PE5PVB/SI4684-DAB-Receiver/src/Si468xROM.h

const PROGMEM unsigned char rom_patch_016[] = {
	0x10, 0x00, 0x00, 0xff, 0x00, 0x00, 0x00, 0x00, 0x00, 0x00, 0x00, 0x00, 0x78, 0x56, 0x34, 0x12, 
	0x00, 0x00, 0x00, 0x00, 0x00, 0x00, 0x00, 0x00, 0xfd, 0x84, 0xcb, 0x6c, 0x01, 0x00, 0x00, 0x00, 
	0xef, 0xbe, 0xad, 0xde, 0x48, 0x16, 0x00, 0x00, 0x04, 0x00, 0x00, 0x00, 0x04, 0x00, 0x00, 0x00, 
	0x00, 0x00, 0x00, 0x00, 0x44, 0x05, 0x20, 0x50, 0x00, 0x00, 0x00, 0x00, 0x00, 0x00, 0x00, 0x00, 
	0x00, 0x00, 0x00, 0x00, 0x00, 0x00, 0x00, 0x00, 0x00, 0x00, 0x00, 0x00, 0x00, 0x00, 0x00, 0x00, 
	0x00, 0x00, 0x00, 0x00, 0x88, 0xcf, 0x6f, 0x07, 0x6f, 0x00, 0x00, 0x81, 0x00, 0xd8, 0x00, 0x50, 
	0x48, 0xe0, 0x00, 0x50, 0x50, 0xe1, 0x00, 0x50, 0x00, 0x2a, 0x00, 0x50, 0xac, 0x67, 0x28, 0x50, 
	0x6c, 0x65, 0x28, 0x50, 0x00, 0x2e, 0x00, 0xa0, 0x80, 0x2a, 0x00, 0x50, 0xa0, 0x96, 0x28, 0x50, 
	0x0c, 0xff, 0xf0, 0xff, 0x00, 0x1e, 0x00, 0xa0, 0x80, 0xff, 0xff, 0x4f, 0xe8, 0x95, 0x28, 0x50, 
	0x40, 0x00, 0x00, 0x50, 0xf8, 0x92, 0x28, 0x50, 0x50, 0x00, 0x00, 0x50, 0x60, 0x00, 0x00, 0x50, 
	0x00, 0x00, 0xff, 0xff, 0x03, 0x10, 0x00, 0x00, 0xa8, 0x08, 0x20, 0x50, 0xc8, 0x08, 0x20, 0x50, 
	0x74, 0x08, 0x20, 0x50, 0xe0, 0x07, 0x20, 0x50, 0xf0, 0x09, 0x20, 0x50, 0x60, 0x06, 0x20, 0x50, 
	0x00, 0xfe, 0x00, 0x50, 0x03, 0x04, 0x20, 0x90, 0xfc, 0x08, 0x20, 0x50, 0x78, 0x67, 0x28, 0x50, 
	0x50, 0x2a, 0x00, 0x50, 0x00, 0x22, 0x00, 0x50, 0xff, 0xff, 0x1f, 0x50, 0x00, 0x00, 0x26, 0x50, 
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
	0x43, 0x54, 0x4e, 0x3e, 0x0a, 0x00, 0x00, 0x00, 0x42, 0x00, 0x00, 0x21, 0x48, 0xe0, 0x00, 0x50, 
	0x0a, 0x05, 0x00, 0x80, 0x00, 0x04, 0x20, 0x50, 0x36, 0x41, 0x00, 0x21, 0x02, 0x32, 0xc0, 0x20, 
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
};
// End of Block 1


  
