PE5PVB/SI4684-DAB-Receiver/src/si4684.h

// Driver for the Skyworks (formerly Silicon Labs) SI4684 DAB+ receiver chip.
//
// Communicates over SPI (pins set up in begin()). Boots the chip by uploading
// the rom-patch + firmware blob, then exposes high-level operations:
//   - tune to a DAB Band III channel
//   - enumerate the services in the current ensemble
//   - select a service and start audio
//   - decode Dynamic Label / Radiotext, PTY, ECC, time, etc.
//   - reassemble MOT slideshow images into /slideshow.img on LittleFS
//
// All chip status comes back via the SPI status byte + a 4 KB SPI rx buffer
// (`SPIbuffer` in si4684.cpp). Every command goes via cts() to wait for the
// "command ready" bit before the next byte is written.

#ifndef si4684_h
#define si4684_h

#include "Arduino.h"
#include <LittleFS.h>
#include "Si468xROM.h"
#include "firmware.h"
#include <SPI.h>
#include <cstring>
#include <climits>

struct DABFrequencyLabel_DAB {
  uint32_t frequency;
  const char* label;
};

const DABFrequencyLabel_DAB DABfrequencyTable_DAB[] = {
  { 174928,  "5A"}, { 176640,  "5B"}, { 178352,  "5C"}, { 180064,  "5D"},
  { 181936,  "6A"}, { 183648,  "6B"}, { 185360,  "6C"}, { 187072,  "6D"},
  { 188928,  "7A"}, { 190640,  "7B"}, { 192352,  "7C"}, { 194064,  "7D"},
  { 195936,  "8A"}, { 197648,  "8B"}, { 199360,  "8C"}, { 201072,  "8D"},
  { 202928,  "9A"}, { 204640,  "9B"}, { 206352,  "9C"}, { 208064,  "9D"},
  { 209936, "10A"}, { 211648, "10B"}, { 213360, "10C"}, { 215072, "10D"},
  { 216928, "11A"}, { 218640, "11B"}, { 220352, "11C"}, { 222064, "11D"},
  { 223936, "12A"}, { 225648, "12B"}, { 227360, "12C"}, { 229072, "12D"},
  { 230784, "13A"}, { 232496, "13B"}, { 234208, "13C"}, { 235776, "13D"},
  { 237488, "13E"}, { 239200, "13F"}
};


static const char* const ProtectionText[] {
  "",
  "UEP-1",
  "UEP-2",
  "UEP-3",
  "UEP-4",
  "UEP-5",
  "EEP-A1",
  "EEP-A2",
  "EEP-A3",
  "EEP-A4",
  "EEP-B1",
  "EEP-B2",
  "EEP-B3",
  "EEP-B4"
};

static const char* const AudioModeText[] {
  "Dual",
  "Mono",
  "Stereo",
  "Joint stereo"
};

static const char* const ServiceTypeText[] {
  "TPEG",
  "Data",
  "FIDC",
  "MSC",
  "DAB+",
  "DAB",
  "FIC",
  "XPAD",
  "-",
  ""
};

// One row of the in-memory service table populated by ServiceInfo().
// Only one CompID per service is stored; secondary components (e.g. data
// streams in the same service) are intentionally ignored.
typedef struct _Services {
  uint32_t  ServiceID;
  uint32_t  CompID;
  char      Label[17];
  byte    ServiceType;
} DABService;

class DAB {
  public:
    bool begin(uint8_t SSpin);
    bool BufferSlideShow;
    bool panic(void);
    bool ServiceStart;
    bool signallock;
    bool SlideShowAvailable;
    bool SlideShowDebug;
    bool SlideShowUpdate;
    bool SlideShowUpdate2;
    char EID[5];
    char EnsembleLabel[17];
    char PStext[17];
    char ServiceData[128];
    char SID[5];
    char* getChipID(void);
    char* getFirmwareVersion(void);
    const char* getChannel(uint8_t freq);
    DABService service[32];
    String ASCII(const char* input, uint8_t charset);
    uint16_t bitrate;
    uint16_t ecc;
    uint16_t ensembleEcc;
    bool serviceHasOwnEcc;
    uint16_t getRSSI(void);
    uint16_t samplerate;
    uint16_t Year;
    uint32_t getFreq(uint8_t freq);
    uint32_t SlideShowLength;
    uint8_t audiomode;
    uint8_t cnr;
    uint8_t Days;
    uint8_t EnsembleLabelCharset;
    uint8_t fic;
    uint8_t getFIC(void);
    uint8_t Hours;
    uint8_t Minutes;
    uint8_t Months;
    uint8_t numberofservices = 0;
    uint8_t protectionlevel;
    uint8_t pty;
    uint8_t Seconds;
    uint8_t ServiceIndex;
    uint8_t ServiceLabelCharset;
    uint8_t servicetype;
    void clearData(void);
    void EnsembleInfo(void);
    void getServiceData(void);
    void ServiceInfo(void);
    void setFreq(uint8_t freq_index);
    void setService(uint8_t index);
    void Update(void);
    void vol(uint8_t vol);

  private:
    bool SlideShowInit;
    bool SlideShowNew;
    bool SlideShowRecover;
    char ChipType[7];
    char FirmwVersion[6];
    bool deleteOldestSlideshow(void);
    bool ensureFreeSpace(size_t requiredBytes);
    String getDynamicFilename(void);
    uint32_t componentID;
    uint32_t CurrentServiceID;
    uint32_t dataServiceCheck;
    uint32_t serviceID;
    uint32_t SlideShowByteCounter;
    uint32_t SlideShowLengthOld;

    // Segment buffering for faster slideshow assembly
    uint8_t SlideShowSegmentBitmap[32];  // Bitmap for up to 256 segments
    uint8_t SlideShowTotalSegments;       // Total segments expected (0 = unknown)
    uint8_t SlideShowHighestSegment;      // Highest segment number seen
    uint16_t SlideShowTransportID;        // Current transport ID
    uint32_t SlideShowLastActivity;       // millis() of last new segment received

    // RAM-based segment buffer (replaces /seg_N.bin files for speed).
    // 80 segments * 512 bytes = 40 KB. Practical DAB MOT segments are 501 bytes.
    // Sized to leave a few KB of DRAM headroom for future Arduino-core upgrades.
    static const uint8_t  SLS_MAX_SEGMENTS  = 80;
    static const uint16_t SLS_MAX_SEG_SIZE  = 512;
    uint8_t  slideshowSegBuf[SLS_MAX_SEGMENTS * SLS_MAX_SEG_SIZE];
    uint16_t slideshowSegLen[SLS_MAX_SEGMENTS];
    void clearSegmentBuffer(void);

    void assembleSlideshow(void);
    bool allSegmentsReceived(void);

    void RecoverSlideShow(void);
};

#endif
