PE5PVB/SI4684-DAB-Receiver/src/gui.cpp

// All TFT rendering. Each Show*() function updates one piece of the screen;
// they only redraw what has actually changed by comparing against a "*Old"
// shadow variable, so the loop can call them all every iteration cheaply.
// BuildDisplay() / BuildChannelList() / BuildMenu() do the full redraws
// when the active view switches.

#include "gui.h"

byte menuitem;                    // current highlight when the menu is open

// Apply the user-selected colour theme to the global PrimaryColor/etc. used
// by every draw routine. Use the linked RGB565 picker to author new themes.
void doTheme(void) {  // Use this to put your own colors in: http://www.barth-dev.de/online/rgb565-color-picker/
  switch (CurrentTheme) {
    case 0:  // Elegant
      PrimaryColor = 0x2e65;
      PrimaryColorSmooth = 0x09a1;
      SecondaryColor = 0x3d7d;
      SecondaryColorSmooth = 0x08e5;
      GreyoutColor = 0x5b0d;
      BackgroundColor = 0x0063;
      BackgroundColor2 = 0x016a;
      BackgroundColor3 = 0x0107;
      BackgroundColor4 = 0x00c6;
      ActiveColor = 0xFFFF;
      ActiveColorSmooth = 0x18E3;
      SignificantColor = 0xF800;
      SignificantColorSmooth = 0x2000;
      InsignificantColor = 0x07E0;
      InsignificantColorSmooth = 0x00C0;
      BarSignificantColor = 0xF800;
      BarInsignificantColor = 0x051f;
      break;

    case 1: // GoldenDusk
      PrimaryColor = 0x8ff1;
      PrimaryColorSmooth = 0x10c2;
      SecondaryColor = 0xFFE0;
      SecondaryColorSmooth = 0x2120;
      GreyoutColor = 0x5b0d;
      BackgroundColor = 0x016b;
      BackgroundColor2 = 0x016a;
      BackgroundColor3 = 0x0107;
      BackgroundColor4 = 0x00c6;
      ActiveColor = 0xFFFF;
      ActiveColorSmooth = 0x18E3;
      SignificantColor = 0xF800;
      SignificantColorSmooth = 0x2000;
      InsignificantColor = 0x07E0;
      InsignificantColorSmooth = 0x00C0;
      BarSignificantColor = 0xF800;
      BarInsignificantColor = 0x07E0;
      break;

    case 2: // Vibrant
      PrimaryColor = 0xF00A;
      PrimaryColorSmooth = 0x3800;
      SecondaryColor = 0xFFE0;
      SecondaryColorSmooth = 0x2120;
      GreyoutColor = 0x5b0d;
      BackgroundColor = 0x016b;
      BackgroundColor2 = 0x016a;
      BackgroundColor3 = 0x0107;
      BackgroundColor4 = 0x00c6;
      ActiveColor = 0x051F;
      ActiveColorSmooth = 0x0106;
      SignificantColor = 0xF3D5;
      SignificantColorSmooth = 0x3008;
      InsignificantColor = 0x07E0;
      InsignificantColorSmooth = 0x00C0;
      BarSignificantColor = 0xF3D5;
      BarInsignificantColor = 0x07E0;
      break;

    case 3: // Serenity
      PrimaryColor = 0xF3D5;
      PrimaryColorSmooth = 0x3008;
      SecondaryColor = 0x9C96;
      SecondaryColorSmooth = 0x41C8;
      GreyoutColor = 0x5b0d;
      BackgroundColor = 0x016b;
      BackgroundColor2 = 0x016a;
      BackgroundColor3 = 0x0107;
      BackgroundColor4 = 0x00c6;
      ActiveColor = 0x9B8D;
      ActiveColorSmooth = 0x5207;
      SignificantColor = 0x748E;
      SignificantColorSmooth = 0x3206;
      InsignificantColor = 0x9B90;
      InsignificantColorSmooth = 0x3946;
      BarSignificantColor = 0x748E;
      BarInsignificantColor = 0xF3D5;
      break;

    case 4: // Luminous
      PrimaryColor = 0x051F;
      PrimaryColorSmooth = 0x0106;
      SecondaryColor = 0xFA8D;
      SecondaryColorSmooth = 0x3083;
      GreyoutColor = 0x5b0d;
      BackgroundColor = 0x016b;
      BackgroundColor2 = 0x016a;
      BackgroundColor3 = 0x0107;
      BackgroundColor4 = 0x00c6;
      ActiveColor = 0xFC00;
      ActiveColorSmooth = 0x3165;
      SignificantColor = 0xFFE0;
      SignificantColorSmooth = 0x2120;
      InsignificantColor = 0xF8C3;
      InsignificantColorSmooth = 0x3800;
      BarSignificantColor = 0xFFE0;
      BarInsignificantColor = 0x867D;
      break;

    case 5: // Radiant
      PrimaryColor = 0x051F;
      PrimaryColorSmooth = 0x0106;
      SecondaryColor = 0xFFE0;
      SecondaryColorSmooth = 0x2120;
      GreyoutColor = 0x5b0d;
      BackgroundColor = 0x016b;
      BackgroundColor2 = 0x016a;
      BackgroundColor3 = 0x0107;
      BackgroundColor4 = 0x00c6;
      ActiveColor = 0xFC00;
      ActiveColorSmooth = 0x3165;
      SignificantColor = 0xFFE0;
      SignificantColorSmooth = 0x2120;
      InsignificantColor = 0xF8C3;
      InsignificantColorSmooth = 0x3800;
      BarSignificantColor = 0xFFE0;
      BarInsignificantColor = 0x867D;
      break;

    case 6: // Sunset
      PrimaryColor = 0x051F;
      PrimaryColorSmooth = 0x0106;
      SecondaryColor = 0xFFE0;
      SecondaryColorSmooth = 0x2120;
      GreyoutColor = 0x5b0d;
      BackgroundColor = 0x016b;
      BackgroundColor2 = 0x016a;
      BackgroundColor3 = 0x0107;
      BackgroundColor4 = 0x00c6;
      ActiveColor = 0xED20;
      ActiveColorSmooth = 0x3940;
      SignificantColor = 0xF800;
      SignificantColorSmooth = 0x2000;
      InsignificantColor = 0x07E0;
      InsignificantColorSmooth = 0x00C0;
      BarSignificantColor = 0xF800;
      BarInsignificantColor = 0x07E0;
      break;
  }
}

// Full-screen overlay listing every metadata field for the current service
// (chip, firmware, ensemble, ECC, PTY, audio mode, bitrate, sample rate).
void ShowServiceInfo(void) {
  setvolume = false;
  displayreset = true;
  tft.pushImage (0, 0, 320, 240, serviceinfobackground);
  tftPrint(0, myLanguage[language][27], 155, 4, ActiveColor, ActiveColorSmooth, 28);
  tftPrint(-1, myLanguage[language][28], 8, 36, ActiveColor, ActiveColorSmooth, 16);
  tftPrint(-1, myLanguage[language][36], 8, 56, ActiveColor, ActiveColorSmooth, 16);
  tftPrint(-1, myLanguage[language][29], 8, 76, ActiveColor, ActiveColorSmooth, 16);
  tftPrint(-1, myLanguage[language][30], 8, 96, ActiveColor, ActiveColorSmooth, 16);
  tftPrint(-1, myLanguage[language][31], 8, 116, ActiveColor, ActiveColorSmooth, 16);
  tftPrint(-1, myLanguage[language][32], 8, 136, ActiveColor, ActiveColorSmooth, 16);
  tftPrint(-1, myLanguage[language][33], 8, 156, ActiveColor, ActiveColorSmooth, 16);
  tftPrint(-1, myLanguage[language][34], 8, 176, ActiveColor, ActiveColorSmooth, 16);
  tftPrint(-1, myLanguage[language][35], 8, 196, ActiveColor, ActiveColorSmooth, 16);

  tftPrint(-1, String(radio.getChannel(dabfreq)) + " - " + String(radio.getFreq(dabfreq) / 1000) + "." + (radio.getFreq(dabfreq) % 1000 < 100 ? "0" : "") + String(radio.getFreq(dabfreq) % 1000) + " MHz", 166, 36, PrimaryColor, PrimaryColorSmooth, 16);
  tftPrint(-1, String(unitString[unit]) + "  MER:", 193, 56, PrimaryColor, PrimaryColorSmooth, 16);
  tftPrint(-1, "dB", 286, 56, PrimaryColor, PrimaryColorSmooth, 16);
  tftPrint(-1, radio.ASCII(radio.EnsembleLabel, radio.EnsembleLabelCharset), 166, 76, PrimaryColor, PrimaryColorSmooth, 16);
  tftPrint(-1, radio.ASCII(radio.service[radio.ServiceIndex].Label, radio.ServiceLabelCharset), 166, 96, PrimaryColor, PrimaryColorSmooth, 16);
  tftPrint(-1, String(radio.pty, DEC) + ": " + String(myLanguage[language][37 + radio.pty]), 166, 116, PrimaryColor, PrimaryColorSmooth, 16);
  tftPrint(-1, ProtectionText[radio.protectionlevel], 166, 136, PrimaryColor, PrimaryColorSmooth, 16);
  String bitrateString = String(radio.samplerate);
  bitrateString = bitrateString.substring(0, 2) + "." + bitrateString.substring(2);
  tftPrint(-1, bitrateString + " Hz", 166, 156, PrimaryColor, PrimaryColorSmooth, 16);
  tftPrint(-1, String(radio.bitrate, DEC) + " kb/s", 166, 176, PrimaryColor, PrimaryColorSmooth, 16);
  tftPrint(-1, String(ServiceTypeText[radio.servicetype]) + " - " + AudioModeText[radio.audiomode], 166, 196, PrimaryColor, PrimaryColorSmooth, 16);
}

// Render the scrollable list of services in the current ensemble. Used as
// the alternative to "main display" when the user opens the channel list.
void BuildChannelList(void) {
  setvolume = false;
  tft.pushImage (0, 0, 320, 240, servicelistbackground);
  tftPrint(0, myLanguage[language][11], 155, 4, ActiveColor, ActiveColorSmooth, 28);

  byte y = 0;
  if (radio.ServiceIndex > 8 && radio.ServiceIndex < 17) {
    y = 9;
  } else if (radio.ServiceIndex > 16 && radio.ServiceIndex < 25) {
    y = 17;
  } else if (radio.ServiceIndex > 24) {
    y = 25;
  }

  if (radio.numberofservices > 8) {
    byte z = 0;
    if (radio.numberofservices < 17) {
      z = 2;
    } else if (radio.numberofservices < 25) {
      z = 3;
    } else if (radio.numberofservices > 24) {
      z = 4;
    }
    if (y == 0) {
      tftPrint(0, "1/" + String(z), 290, 10, SecondaryColor, SecondaryColorSmooth, 16);
    } else if (y == 9) {
      tftPrint(0, "2/" + String(z), 290, 10, SecondaryColor, SecondaryColorSmooth, 16);
    } else if (y == 17) {
      tftPrint(0, "3/" + String(z), 290, 10, SecondaryColor, SecondaryColorSmooth, 16);
    } else if (y == 25) {
      tftPrint(0, "4/" + String(z), 290, 10, SecondaryColor, SecondaryColorSmooth, 16);
    }
  }

  for (byte i = y; i < radio.numberofservices; i++) {
    ShowOneLine(20 * (i - y), i, (radio.ServiceIndex - y == i - y ? true : false));
    if (i - y == 8) i = 254;
  }
}

// Draw one row of a list/menu. `position` is the vertical line slot
// (ITEM1..ITEM10) and `item` is the data row to read from. `selected`
// switches between highlighted vs normal styling.
void ShowOneLine(byte position, byte item, bool selected) {
  if (ChannelListView) {
    FullLineSprite.pushImage (-8, -position - 35, 320, 240, servicelistbackground);
    if (selected) FullLineSprite.pushImage(0, 0, 304, 20, selector);

    FullLineSprite.setTextColor(SecondaryColor, SecondaryColorSmooth, false);
    FullLineSprite.setTextDatum(TL_DATUM);
    FullLineSprite.drawString(String(radio.service[item].CompID & 0xFF, DEC), 12, 3);

    String serviceIDString = String(radio.service[item].ServiceID & 0xFFFF, HEX);
    while (serviceIDString.length() < 4) serviceIDString = "0" + serviceIDString;
    serviceIDString.toUpperCase();
    FullLineSprite.setTextDatum(TC_DATUM);
    FullLineSprite.drawString(serviceIDString, 56, 3);

    FullLineSprite.setTextColor(PrimaryColor, PrimaryColorSmooth, false);
    FullLineSprite.setTextDatum(TL_DATUM);
    FullLineSprite.drawString(String(radio.ASCII(radio.service[item].Label, radio.ServiceLabelCharset)), 84, 3);

    FullLineSprite.setTextDatum(TC_DATUM);
    FullLineSprite.setTextColor(SecondaryColor, SecondaryColorSmooth, false);
    FullLineSprite.drawString(ServiceTypeText[radio.service[item].ServiceType], 282, 3);
    FullLineSprite.pushSprite(8, 35 + position);
  } else if (menu) {
    FullLineSprite.pushImage (-8, -position - 32, 320, 240, configurationbackground);
    if (selected) FullLineSprite.pushImage(0, 0, 304, 20, selector);

    FullLineSprite.setTextDatum(TL_DATUM);
    FullLineSprite.setTextColor(ActiveColor, ActiveColorSmooth, false);
    switch (item) {
      case 0:
        FullLineSprite.drawString(myLanguage[language][12], 6, 3);
        FullLineSprite.setTextDatum(TR_DATUM);
        FullLineSprite.setTextColor(PrimaryColor, PrimaryColorSmooth, false);
        FullLineSprite.drawString(myLanguage[language][0], 300, 3);
        break;

      case 1:
        FullLineSprite.drawString(myLanguage[language][13], 6, 3);
        FullLineSprite.setTextDatum(TR_DATUM);
        FullLineSprite.drawString("%", 300, 3);
        FullLineSprite.setTextColor(PrimaryColor, PrimaryColorSmooth, false);
        FullLineSprite.drawString(String(ContrastSet, DEC), 270, 3);
        break;

      case 2:
        FullLineSprite.drawString(myLanguage[language][14], 6, 3);
        FullLineSprite.setTextDatum(TR_DATUM);
        FullLineSprite.setTextColor(PrimaryColor, PrimaryColorSmooth, false);
        FullLineSprite.drawString(Theme[CurrentTheme], 300, 3);
        break;

      case 3:
        FullLineSprite.drawString(myLanguage[language][15], 6, 3);
        FullLineSprite.setTextDatum(TR_DATUM);
        FullLineSprite.setTextColor(PrimaryColor, PrimaryColorSmooth, false);
        FullLineSprite.drawString((autoslideshow ? myLanguage[language][23] : myLanguage[language][24]), 300, 3);
        break;

      case 4:
        FullLineSprite.drawString(myLanguage[language][16], 6, 3);
        FullLineSprite.setTextDatum(TR_DATUM);
        FullLineSprite.setTextColor(PrimaryColor, PrimaryColorSmooth, false);
        FullLineSprite.drawString(unitString[unit], 300, 3);
        break;

      case 5:
        FullLineSprite.drawString(myLanguage[language][25], 6, 3);
        FullLineSprite.setTextColor(PrimaryColor, PrimaryColorSmooth, false);
        FullLineSprite.setTextDatum(TR_DATUM);
        FullLineSprite.drawString((tot != 0 ? String(tot) : ""), 270, 3);
        if (tot != 0) FullLineSprite.setTextColor(ActiveColor, ActiveColorSmooth, false);
        FullLineSprite.drawString((tot != 0 ? myLanguage[language][26] : myLanguage[language][24]), 300, 3);
        break;

	  case 6:
        FullLineSprite.drawString(myLanguage[language][17], 6, 3);
        FullLineSprite.setTextDatum(TR_DATUM);
        FullLineSprite.setTextColor(PrimaryColor, PrimaryColorSmooth, false);
        FullLineSprite.drawString((radio.BufferSlideShow ? myLanguage[language][23] : myLanguage[language][24]), 300, 3);
        break;
	  

      case 8:
        FullLineSprite.drawString(myLanguage[language][81], 6, 3);
        FullLineSprite.setTextDatum(TR_DATUM);
        break;
    }
    FullLineSprite.pushSprite(8, 32 + position);
  }
}

// Full redraw of the settings menu (entered by long-pressing MODE).
void BuildMenu(void) {
  SlideShowView = false;
  ShowServiceInformation = false;
  ChannelListView = false;

  tft.pushImage (0, 0, 320, 240, configurationbackground);
  tftPrint(0, myLanguage[language][20], 155, 4, PrimaryColor, PrimaryColorSmooth, 28);
  tftPrint(0, myLanguage[language][19], 155, 222, SecondaryColor, SecondaryColorSmooth, 16);

  ShowOneLine(ITEM1, 0, (menuoption == ITEM1 ? true : false));
  ShowOneLine(ITEM2, 1, (menuoption == ITEM2 ? true : false));
  ShowOneLine(ITEM3, 2, (menuoption == ITEM3 ? true : false));
  ShowOneLine(ITEM4, 3, (menuoption == ITEM4 ? true : false));
  ShowOneLine(ITEM5, 4, (menuoption == ITEM5 ? true : false));
  ShowOneLine(ITEM6, 5, (menuoption == ITEM6 ? true : false));
  ShowOneLine(ITEM7, 6, (menuoption == ITEM7 ? true : false));
  ShowOneLine(ITEM8, 7, (menuoption == ITEM8 ? true : false));
  ShowOneLine(ITEM9, 8, (menuoption == ITEM9 ? true : false));
}

// Full redraw of the main radio screen (frequency, PS, RT, signal bars,
// memory slot, clock). Called when switching back from another view or
// after a theme/display-orientation change.
void BuildDisplay(void) {
  SlideShowView = false;
  ShowServiceInformation = false;
  ChannelListView = false;
  displayreset = true;
  setvolume = false;
  rotary = 0;
  rotary2 = 0;

  tft.pushImage (0, 0, 320, 240, Background);
  tftPrint(1, "PR:", 84, 65, ActiveColor, ActiveColorSmooth, 16);
  tftPrint(-1, "EID", 10, 105, ActiveColor, ActiveColorSmooth, 16);
  tftPrint(-1, "SID", 10, 120, ActiveColor, ActiveColorSmooth, 16);
  tftPrint(1, "MHz", 310, 55, ActiveColor, ActiveColorSmooth, 16);
  tftPrint(-1, "SIG:", 123, 109, ActiveColor, ActiveColorSmooth, 16);
  tftPrint(-1, unitString[unit], 183, 109, ActiveColor, ActiveColorSmooth, 16);
  tftPrint(-1, "MER:", 237, 109, ActiveColor, ActiveColorSmooth, 16);
  tftPrint(1, "dB", 309, 109, ActiveColor, ActiveColorSmooth, 16);
  tftPrint(-1, "Q", 122, 90, ActiveColor, ActiveColorSmooth, 16);
  tftPrint(-1, "S", 122, 127, SecondaryColor, SecondaryColorSmooth, 16);
  tftPrint(1, "ECC", 110, 90, ActiveColor, ActiveColorSmooth, 16);

  for (byte segments = 0; segments < 13; segments++) tft.fillRect(134 + (segments * 14), 135, 2, 3, (segments < 8 ? BarInsignificantColor : BarSignificantColor));
  tft.drawLine(134, 138, 302, 138, ActiveColor);
  tftPrint(-1, "1   3   5   7   9  +10 +30", 134, 140, ActiveColor, ActiveColorSmooth, 16);
  tft.drawRect(134, 90, 141, 12, GreyoutColor);

  ShowFreq();
  ShowTuneMode();
  ShowMemoryPos();
}

// Menu navigation: handle the rotary-up event while the settings menu is
// open. Either steps a value of the current row or moves to the next row.
void MenuUp(void) {
  if (!menuopen) {
    ShowOneLine(menuoption, menuitem, false);
    menuoption += ITEM_GAP;
    menuitem++;
    if (menuitem > 6 && menuitem < 8) {
      menuitem = 8;
      menuoption = ITEM9;
    } else if (menuitem > 8) {
      menuitem = 0;
      menuoption = ITEM1;
    }
    ShowOneLine(menuoption, menuitem, true);
  } else {
    OneBigLineSprite.pushImage(-11, -88, 292, 170, popupbackground);
    OneBigLineSprite.setTextColor(PrimaryColor, PrimaryColorSmooth, false);
    OneBigLineSprite.setTextDatum(TC_DATUM);

    switch (menuoption) {
      case ITEM1:
        language ++;
        if (language == (sizeof (myLanguage) / sizeof (myLanguage[0]))) language = 0;
        OneBigLineSprite.drawString(myLanguage[language][0], 135, 2);
        OneBigLineSprite.pushSprite(24, 118);
        break;

      case ITEM2:
        ContrastSet ++;
        if (ContrastSet > 100) ContrastSet = 1;
        OneBigLineSprite.setTextDatum(TL_DATUM);
        OneBigLineSprite.setTextColor(ActiveColor, ActiveColorSmooth, false);
        OneBigLineSprite.drawString("%", 155, 2);
        OneBigLineSprite.setTextDatum(TR_DATUM);
        OneBigLineSprite.setTextColor(PrimaryColor, PrimaryColorSmooth, false);
        OneBigLineSprite.drawString(String(ContrastSet, DEC), 135, 2);
        analogWrite(CONTRASTPIN, ContrastSet * 2 + 27);
        OneBigLineSprite.pushSprite(24, 118);
        break;

      case ITEM3:
        CurrentTheme ++;
        if (CurrentTheme > sizeof(Theme) / sizeof(Theme[0]) - 1) CurrentTheme = 0;
        doTheme();
        tft.pushImage (13, 30, 292, 170, popupbackground);
        Infoboxprint(myLanguage[language][14]);
        OneBigLineSprite.setTextColor(PrimaryColor, PrimaryColorSmooth, false);
        OneBigLineSprite.drawString(Theme[CurrentTheme], 135, 2);
        OneBigLineSprite.pushSprite(24, 118);
        break;

      case ITEM4:
        if (autoslideshow) autoslideshow = false; else autoslideshow = true;
        OneBigLineSprite.drawString((autoslideshow ? myLanguage[language][23] : myLanguage[language][24]), 135, 2);
        OneBigLineSprite.pushSprite(24, 118);
        break;

      case ITEM5:
        unit ++;
        if (unit > sizeof(unitString) / sizeof(unitString[0]) - 1) unit = 0;
        OneBigLineSprite.drawString(unitString[unit], 135, 2);
        OneBigLineSprite.pushSprite(24, 118);
        break;

      case ITEM6:
        switch (tot) {
          case 0: tot = 15; break;
          case 15: tot = 30; break;
          case 30: tot = 60; break;
          case 60: tot = 90; break;
          default: tot = 0; break;
        }
        if (tot != 0) {
          OneBigLineSprite.setTextDatum(TR_DATUM);
          OneBigLineSprite.drawString(String(tot), 135, 2);
          OneBigLineSprite.setTextColor(ActiveColor, ActiveColorSmooth, false);
          OneBigLineSprite.setTextDatum(TL_DATUM);
          OneBigLineSprite.drawString(myLanguage[language][26], 155, 2);
        } else {
          OneBigLineSprite.drawString(myLanguage[language][24], 135, 2);
        }
        OneBigLineSprite.pushSprite(24, 118);
        break;
		
      case ITEM7:
        radio.BufferSlideShow = !radio.BufferSlideShow;
        OneBigLineSprite.drawString((radio.BufferSlideShow ? myLanguage[language][23] : myLanguage[language][24]), 135, 2);
        OneBigLineSprite.pushSprite(24, 118);
        break;		
    }
  }
}

// Menu navigation: rotary-down counterpart of MenuUp().
void MenuDown(void) {
  if (!menuopen) {
    ShowOneLine(menuoption, menuitem, false);
    menuoption -= ITEM_GAP;
    menuitem--;
    if (menuitem < 8 && menuitem > 6) {
      menuoption = ITEM7;
      menuitem = 6;
    } else if (menuitem > 8) {
      menuoption = ITEM9;
      menuitem = 8;
    }
    ShowOneLine(menuoption, menuitem, true);
  } else {
    OneBigLineSprite.pushImage(-11, -88, 292, 170, popupbackground);
    OneBigLineSprite.setTextColor(PrimaryColor, PrimaryColorSmooth, false);
    OneBigLineSprite.setTextDatum(TC_DATUM);

    switch (menuoption) {
      case ITEM1:
        language --;
        if (language > (sizeof (myLanguage) / sizeof (myLanguage[0]))) language = (sizeof (myLanguage) / sizeof (myLanguage[0])) - 1;
        OneBigLineSprite.drawString(myLanguage[language][0], 135, 2);
        OneBigLineSprite.pushSprite(24, 118);
        break;

      case ITEM2:
        ContrastSet --;
        if (ContrastSet < 1) ContrastSet = 100;
        OneBigLineSprite.setTextDatum(TL_DATUM);
        OneBigLineSprite.setTextColor(ActiveColor, ActiveColorSmooth, false);
        OneBigLineSprite.drawString("%", 155, 2);

        OneBigLineSprite.setTextDatum(TR_DATUM);
        OneBigLineSprite.setTextColor(PrimaryColor, PrimaryColorSmooth, false);
        OneBigLineSprite.drawString(String(ContrastSet, DEC), 135, 2);
        analogWrite(CONTRASTPIN, ContrastSet * 2 + 27);
        OneBigLineSprite.pushSprite(24, 118);
        break;

      case ITEM3:
        CurrentTheme --;
        if (CurrentTheme > sizeof(Theme) / sizeof(Theme[0]) - 1) CurrentTheme = sizeof(Theme) / sizeof(Theme[0]) - 1;
        doTheme();
        tft.pushImage (13, 30, 292, 170, popupbackground);
        Infoboxprint(myLanguage[language][14]);
        OneBigLineSprite.setTextColor(PrimaryColor, PrimaryColorSmooth, false);
        OneBigLineSprite.drawString(Theme[CurrentTheme], 135, 2);
        OneBigLineSprite.pushSprite(24, 118);
        break;

      case ITEM4:
        if (autoslideshow) autoslideshow = false; else autoslideshow = true;
        OneBigLineSprite.drawString((autoslideshow ? myLanguage[language][23] : myLanguage[language][24]), 135, 2);
        OneBigLineSprite.pushSprite(24, 118);
        break;

      case ITEM5:
        unit --;
        if (unit > sizeof(unitString) / sizeof(unitString[0]) - 1) unit = sizeof(unitString) / sizeof(unitString[0]) - 1;
        OneBigLineSprite.drawString(unitString[unit], 135, 2);
        OneBigLineSprite.pushSprite(24, 118);
        break;

      case ITEM6:
        switch (tot) {
          case 15: tot = 0; break;
          case 30: tot = 15; break;
          case 60: tot = 30; break;
          case 90: tot = 60; break;
          default: tot = 90; break;
        }
        if (tot != 0) {
          OneBigLineSprite.setTextDatum(TR_DATUM);
          OneBigLineSprite.drawString(String(tot), 135, 2);
          OneBigLineSprite.setTextColor(ActiveColor, ActiveColorSmooth, false);
          OneBigLineSprite.setTextDatum(TL_DATUM);
          OneBigLineSprite.drawString(myLanguage[language][26], 155, 2);
        } else {
          OneBigLineSprite.drawString(myLanguage[language][24], 135, 2);
        }
        OneBigLineSprite.pushSprite(24, 118);
        break;
		
      case ITEM7:
        radio.BufferSlideShow = !radio.BufferSlideShow;
        OneBigLineSprite.drawString((radio.BufferSlideShow ? myLanguage[language][23] : myLanguage[language][24]), 135, 2);
        OneBigLineSprite.pushSprite(24, 118);
        break;			
    }
  }
}

// Menu confirm: rotary-button click while in the menu. Either enters a sub-
// menu, applies the current change, or commits the value to EEPROM.
void DoMenu(void) {
  if (!menuopen) {
    tft.pushImage (13, 30, 292, 170, popupbackground);
    OneBigLineSprite.pushImage(-11, -88, 292, 170, popupbackground);
    OneBigLineSprite.setTextColor(PrimaryColor, PrimaryColorSmooth, false);
    OneBigLineSprite.setTextDatum(TC_DATUM);
    menuopen = true;

    switch (menuoption) {
      case ITEM1:
        Infoboxprint(myLanguage[language][12]);
        OneBigLineSprite.drawString(myLanguage[language][0], 135, 2);
        OneBigLineSprite.pushSprite(24, 118);
        break;

      case ITEM2:
        Infoboxprint(myLanguage[language][13]);
        OneBigLineSprite.setTextDatum(TL_DATUM);
        OneBigLineSprite.setTextColor(ActiveColor, ActiveColorSmooth, false);
        OneBigLineSprite.drawString("%", 155, 2);

        OneBigLineSprite.setTextDatum(TR_DATUM);
        OneBigLineSprite.setTextColor(PrimaryColor, PrimaryColorSmooth, false);
        OneBigLineSprite.drawString(String(ContrastSet, DEC), 135, 2);
        OneBigLineSprite.pushSprite(24, 118);
        break;

      case ITEM3:
        Infoboxprint(myLanguage[language][14]);
        OneBigLineSprite.drawString(Theme[CurrentTheme], 135, 2);
        OneBigLineSprite.pushSprite(24, 118);
        break;

      case ITEM4:
        Infoboxprint(myLanguage[language][15]);
        OneBigLineSprite.drawString((autoslideshow ? myLanguage[language][23] : myLanguage[language][24]), 135, 2);
        OneBigLineSprite.pushSprite(24, 118);
        break;

      case ITEM5:
        Infoboxprint(myLanguage[language][16]);
        OneBigLineSprite.drawString(unitString[unit], 135, 2);
        OneBigLineSprite.pushSprite(24, 118);
        break;

      case ITEM6:
        Infoboxprint(myLanguage[language][25]);
        if (tot != 0) {
          OneBigLineSprite.setTextDatum(TR_DATUM);
          OneBigLineSprite.drawString(String(tot), 135, 2);
          OneBigLineSprite.setTextColor(ActiveColor, ActiveColorSmooth, false);
          OneBigLineSprite.setTextDatum(TL_DATUM);
          OneBigLineSprite.drawString(myLanguage[language][26], 155, 2);
        } else {
          OneBigLineSprite.drawString(myLanguage[language][24], 135, 2);
        }
        OneBigLineSprite.pushSprite(24, 118);
        break;

      case ITEM7:
        Infoboxprint(myLanguage[language][17]);
        OneBigLineSprite.drawString((radio.BufferSlideShow ? myLanguage[language][23] : myLanguage[language][24]), 135, 2);
        OneBigLineSprite.pushSprite(24, 118);
        break;

      case ITEM9:
        tftPrint(0, myLanguage[language][79], 155, 40, ActiveColor, ActiveColorSmooth, 28);
        tftPrint(0, "PE5PVB", 155, 72, PrimaryColor, PrimaryColorSmooth, 28);
        tftPrint(0, myLanguage[language][80], 155, 108, ActiveColor, ActiveColorSmooth, 28);
        tftPrint(0, "mcelliotg", 155, 138, PrimaryColor, PrimaryColorSmooth, 28);
        tftPrint(0, "github.com/PE5PVB/SI4684-DAB-Receiver", 155, 175, SecondaryColor, SecondaryColorSmooth, 16);
        break;
    }
  } else {
    menuopen = false;
    BuildMenu();
  }
}

// Render a centered text line in the small "info" box at the top of the
// screen (used for transient messages like "Saved" / "No signal").
void Infoboxprint(const char* input) {
  int length = strlen(input);
  int newlineIndex = -1;

  for (int i = 0; i < length; i++) {
    if (input[i] == '\n') {
      newlineIndex = i;
      break;
    }
  }

  if (newlineIndex != -1) {
    char* line1 = (char*)malloc((newlineIndex + 1) * sizeof(char));
    strncpy(line1, input, newlineIndex);
    line1[newlineIndex] = '\0';

    char* line2 = (char*)malloc((length - newlineIndex) * sizeof(char));
    strcpy(line2, input + newlineIndex + 1);

    tftPrint(0, line1, 155, 48, ActiveColor, ActiveColorSmooth, 28);
    tftPrint(0, line2, 155, 78, ActiveColor, ActiveColorSmooth, 28);
    free(line1);
    free(line2);
  } else {
    tftPrint(0, input, 155, 78, ActiveColor, ActiveColorSmooth, 28);
  }
}

// The Show*() routines below are individually called from ProcessDAB() every
// loop. Each one diffs the current radio.* / live state against a `*Old` shadow
// variable and only pushes its sprite/region to the TFT when something changed.

void ShowFreq(void) {
  tftReplace(0, radio.getChannel(dabfreqold), radio.getChannel(dabfreq), 145, 45, PrimaryColor, PrimaryColorSmooth, BackgroundColor2, 28);
  tftReplace(-1, dabfreqStringOld, String(radio.getFreq(dabfreq) / 1000) + "." + (radio.getFreq(dabfreq) % 1000 < 100 ? "0" : "") + String(radio.getFreq(dabfreq) % 1000), 184, 43, SecondaryColor, SecondaryColorSmooth, BackgroundColor2, 52);
  dabfreqStringOld = String(radio.getFreq(dabfreq) / 1000) + "." + (radio.getFreq(dabfreq) % 1000 < 100 ? "0" : "") + String(radio.getFreq(dabfreq) % 1000);
  dabfreqold = dabfreq;
}

void ShowPTY(void) {
  if (!radio.ServiceStart) radio.pty = 36;
  if (radio.pty != ptyold || displayreset) {
    LongSprite.pushImage(-8, -162, 320, 240, Background);
    LongSprite.setTextDatum(TC_DATUM);
    LongSprite.setTextColor(SecondaryColor, SecondaryColorSmooth, false);
    LongSprite.drawString(myLanguage[language][37 + radio.pty], 75, 0);
    LongSprite.pushSprite(8, 162);
    ptyold = radio.pty;
  }
}

void ShowRT(void) {
  if (ShowServiceInformation)  {
    FullLineSprite.pushImage(-6, -220, 320, 240, serviceinfobackground);
  } else if (ChannelListView) {
    FullLineSprite.pushImage(-6, -220, 320, 240, servicelistbackground);
  } else {
    FullLineSprite.pushImage(-6, -220, 320, 240, Background);
  }

  FullLineSprite.setTextColor(PrimaryColor, PrimaryColorSmooth, false);
  if (radio.ASCII(radio.ServiceData, radio.ServiceLabelCharset).length() > 0) {
    RTWidth = tft.textWidth(radio.ASCII(radio.ServiceData, radio.ServiceLabelCharset));
    if (RTWidth < 300) {
      xPos = 0;
      FullLineSprite.setTextDatum(TC_DATUM);
      FullLineSprite.drawString(String(radio.ASCII(radio.ServiceData, radio.ServiceLabelCharset)), 154, 1);
      FullLineSprite.pushSprite(6, 219);
    } else {
      if (millis() - rtticker >= 20) {
        xPos --;
        rttickerhold = millis();

        if (xPos < -RTWidth - 50) xPos = 0;
        FullLineSprite.setTextDatum(TL_DATUM);
        FullLineSprite.drawString(String(radio.ASCII(radio.ServiceData, radio.ServiceLabelCharset)), xPos, 1);
        FullLineSprite.drawString(String(radio.ASCII(radio.ServiceData, radio.ServiceLabelCharset)), xPos + RTWidth + 50, 1);
        FullLineSprite.pushSprite(6, 219);
        rtticker = millis();
      }
    }
  } else {
    FullLineSprite.pushSprite(6, 220);
  }
  if (RTold != radio.ASCII(radio.ServiceData, radio.ServiceLabelCharset)) xPos = 0;
  RTold = radio.ASCII(radio.ServiceData, radio.ServiceLabelCharset);
}

void ShowSID(void) {
  if (!radio.ServiceStart) radio.SID[0] = '\0';
  if (String(radio.SID) != SIDold || displayreset) {
    ShortSprite.pushImage(-38, -120, 320, 240, Background);
    ShortSprite.setTextDatum(TL_DATUM);
    ShortSprite.setTextColor(SecondaryColor, SecondaryColorSmooth, false);
    ShortSprite.drawString(String(radio.SID), 0, 0);
    ShortSprite.pushSprite(38, 120);
    SIDold = String(radio.SID);
  }
}

void ShowEID(void) {
  if (tuning) radio.EID[0] = '\0';
  if (String(radio.EID) != EIDold || displayreset) {
    ShortSprite.pushImage(-38, -106, 320, 240, Background);
    ShortSprite.setTextDatum(TL_DATUM);
    ShortSprite.setTextColor(SecondaryColor, SecondaryColorSmooth, false);
    ShortSprite.drawString(String(radio.EID), 0, 0);
    ShortSprite.pushSprite(38, 106);
    EIDold = String(radio.EID);
  }
}

void ShowPS(void) {
  if (tunemode != TUNE_MEM && !radio.ServiceStart && !tuning && !seek) {
    if (radio.signallock && !radio.ServiceStart) {
      strncpy(_serviceName, (radio.numberofservices > 0 ? myLanguage[language][74] : myLanguage[language][73]), sizeof(_serviceName));
      _serviceName[sizeof(_serviceName) - 1] = '\0';
    } else if (radio.signallock && radio.ServiceStart) {
      for (byte x = 0; x < 16; x++) _serviceName[x] = '\0';
    } else if (!trysetservice) {
      for (byte x = 0; x < 16; x++) _serviceName[x] = '\0';
    }
  } else if (tunemode != TUNE_MEM && !tuning) {
    strcpy(_serviceName, radio.service[radio.ServiceIndex].Label);
  }

  if ((radio.ServiceStart ? radio.ASCII(radio.service[radio.ServiceIndex].Label, radio.ServiceLabelCharset) : radio.ASCII(_serviceName, radio.ServiceLabelCharset)) != PSold || displayreset) {
    if (tunemode != TUNE_MEM || (tunemode == TUNE_MEM && String((radio.signallock && radio.ServiceStart ? radio.ASCII(radio.PStext, radio.ServiceLabelCharset) : radio.ASCII(_serviceName, radio.ServiceLabelCharset))).length() != 0)) {
      OneBigLineSprite.pushImage(-44, -185, 320, 240, Background);
      OneBigLineSprite.setTextColor(SecondaryColor, SecondaryColorSmooth, false);
      OneBigLineSprite.setTextDatum(TC_DATUM);
      OneBigLineSprite.setTextColor(SecondaryColor, SecondaryColorSmooth, false);
      OneBigLineSprite.drawString(String((radio.ServiceStart ? radio.ASCII(radio.PStext, radio.ServiceLabelCharset) : (radio.signallock && tunemode != TUNE_MEM && !tuning && !seek ? (radio.numberofservices > 0 ? myLanguage[language][74] : myLanguage[language][73]) : radio.ASCII(_serviceName, radio.ServiceLabelCharset)))), 130, 4);
      OneBigLineSprite.pushSprite(44, 185);
    }
    PSold = (radio.ServiceStart ? radio.ASCII(radio.PStext, radio.ServiceLabelCharset) : radio.ASCII(_serviceName, radio.ServiceLabelCharset));
  }
}

void ShowEN(void) {
  if (tuning) {
    strncpy(radio.EnsembleLabel, myLanguage[language][75], sizeof(radio.EnsembleLabel));
    radio.EnsembleLabel[sizeof(radio.EnsembleLabel) - 1] = '\0';
  } else if (!radio.signallock) {
    strncpy(radio.EnsembleLabel, myLanguage[language][76], sizeof(radio.EnsembleLabel));
    radio.EnsembleLabel[sizeof(radio.EnsembleLabel) - 1] = '\0';
  }

  if (EnsembleNameOld != radio.ASCII(radio.EnsembleLabel, radio.EnsembleLabelCharset) || displayreset) {
    tft.fillRect(167, 162, 145, 16, BackgroundColor4);
    if (tuning || !radio.signallock) {
      if (tuning) {
        tftPrint(0, myLanguage[language][75], 238, 162, SecondaryColor, SecondaryColorSmooth, 16);
      } else if (!radio.signallock) {
        tftPrint(0, myLanguage[language][76], 238, 162, SecondaryColor, SecondaryColorSmooth, 16);
      }
    } else {
      tftPrint(0, radio.ASCII(radio.EnsembleLabel, radio.EnsembleLabelCharset), 238, 162, SecondaryColor, SecondaryColorSmooth, 16);
    }
    EnsembleNameOld = radio.ASCII(radio.EnsembleLabel, radio.EnsembleLabelCharset);

  }
  if (!radio.signallock || tuning) radio.EnsembleLabel[0] = '\0';
}

void ShowProtectionlevel(void) {
  if (!radio.ServiceStart) radio.protectionlevel = 0;
  if (String(ProtectionText[radio.protectionlevel]) != PLold || displayreset) {
    MediumSprite.pushImage(-9, -90, 320, 240, Background);
    MediumSprite.setTextDatum(TC_DATUM);
    MediumSprite.setTextColor(PrimaryColor, PrimaryColorSmooth, false);
    MediumSprite.drawString(String(ProtectionText[radio.protectionlevel]), 30, 0);
    MediumSprite.pushSprite(9, 90);
    PLold = String(ProtectionText[radio.protectionlevel]);
  }
}

void ShowAudioMode(void) {
  if (!radio.ServiceStart) radio.servicetype = 9;
  if (servicetypeold != radio.servicetype || displayreset) {
    tftPrint(-1, ServiceTypeText[4], 70, 33, GreyoutColor, BackgroundColor, 16);
    if (radio.servicetype == 4 || radio.servicetype == 5) tftPrint(-1, ServiceTypeText[radio.servicetype], 70, 33, SecondaryColor, SecondaryColorSmooth, 16);
    servicetypeold = radio.servicetype;
  }

  if (!radio.ServiceStart) radio.audiomode = 4;
  if (audiomodeold != radio.audiomode || displayreset) {
    switch (radio.audiomode) {
      case 0: tft.pushImage(10, 4, 28, 19, mono); break;
      case 1: tft.pushImage(10, 4, 28, 19, mono); break;
      case 2:
      case 3: tft.pushImage(10, 4, 28, 19, stereoon); break;
      case 4: tft.pushImage(10, 4, 28, 19, stereooff); break;
    }
    audiomodeold = radio.audiomode;
  }
}

void ShowECC(void) {
  if (eccold != radio.ecc || displayreset) {
    String ITU = "";
    switch (radio.serviceHasOwnEcc ? radio.SID[0] : radio.EID[0]) {
      case '1':
        switch (radio.ecc) {
          case 0xe0: tft.pushImage(80, 110, 36, 23, de); ITU = "D"; break;
          case 0xe1: tft.pushImage(80, 110, 36, 23, gr); ITU = "GRC"; break;
          case 0xe2: tft.pushImage(80, 110, 36, 23, ma); ITU = "MRC"; break;
          case 0xe3: tft.pushImage(80, 110, 36, 23, me); ITU = "MNE"; break;
          case 0xe4: tft.pushImage(80, 110, 36, 23, md); ITU = "MDA"; break;
          default: tft.pushImage(80, 110, 36, 23, unknown); ITU = ""; break;
        }
        break;

      case '2':
        switch (radio.ecc) {
          case 0xe0: tft.pushImage(80, 110, 36, 23, dz); ITU = "ALG"; break;
          case 0xe1: tft.pushImage(80, 110, 36, 23, cy); ITU = "CYP"; break;
          case 0xe2: tft.pushImage(80, 110, 36, 23, cz); ITU = "CZE"; break;
          case 0xe3: tft.pushImage(80, 110, 36, 23, ie); ITU = "IRL"; break;
          case 0xe4: tft.pushImage(80, 110, 36, 23, ee); ITU = "EST"; break;
          default: tft.pushImage(80, 110, 36, 23, unknown); ITU = ""; break;
        }
        break;

      case '3':
        switch (radio.ecc) {
          case 0xe0: tft.pushImage(80, 110, 36, 23, ad); ITU = "AND"; break;
          case 0xe1: tft.pushImage(80, 110, 36, 23, sm); ITU = "SM"; break;
          case 0xe2: tft.pushImage(80, 110, 36, 23, pl); ITU = "POL"; break;
          case 0xe3: tft.pushImage(80, 110, 36, 23, tr); ITU = "TUR"; break;
          case 0xe4: tft.pushImage(80, 110, 36, 23, mk); ITU = "MKD"; break;
          default: tft.pushImage(80, 110, 36, 23, unknown); ITU = ""; break;
        }
        break;

      case '4':
        switch (radio.ecc) {
          case 0xe0: tft.pushImage(80, 110, 36, 23, il); ITU = "ISR"; break;
          case 0xe1: tft.pushImage(80, 110, 36, 23, ch); ITU = "SUI"; break;
          case 0xe2: tft.pushImage(80, 110, 36, 23, va); ITU = "CVA"; break;
          default: tft.pushImage(80, 110, 36, 23, unknown); ITU = ""; break;
        }
        break;

      case '5':
        switch (radio.ecc) {
          case 0xe0: tft.pushImage(80, 110, 36, 23, it); ITU = "I"; break;
          case 0xe1: tft.pushImage(80, 110, 36, 23, jo); ITU = "JOR"; break;
          case 0xe2: tft.pushImage(80, 110, 36, 23, sk); ITU = "SVK"; break;
          case 0xe3: tft.pushImage(80, 110, 36, 23, tj); ITU = "TJK"; break;
          default: tft.pushImage(80, 110, 36, 23, unknown); ITU = ""; break;
        }
        break;

      case '6':
        switch (radio.ecc) {
          case 0xe0: tft.pushImage(80, 110, 36, 23, be); ITU = "BEL"; break;
          case 0xe1: tft.pushImage(80, 110, 36, 23, fi); ITU = "FNL"; break;
          case 0xe2: tft.pushImage(80, 110, 36, 23, sy); ITU = "SYR"; break;
          case 0xe4: tft.pushImage(80, 110, 36, 23, ua); ITU = "UKR"; break;
          default: tft.pushImage(80, 110, 36, 23, unknown); ITU = ""; break;
        }
        break;

      case '7':
        switch (radio.ecc) {
          case 0xe0: tft.pushImage(80, 110, 36, 23, ru); ITU = "RUS"; break;
          case 0xe1: tft.pushImage(80, 110, 36, 23, lu); ITU = "LUX"; break;
          case 0xe2: tft.pushImage(80, 110, 36, 23, tn); ITU = "TUN"; break;
          case 0xe4: tft.pushImage(80, 110, 36, 23, kz); ITU = "XXK"; break;
          default: tft.pushImage(80, 110, 36, 23, unknown); ITU = ""; break;
        }
        break;

      case '8':
        switch (radio.ecc) {
          case 0xe0: tft.pushImage(80, 110, 36, 23, ra); ITU = "AZR"; break;
          case 0xe1: tft.pushImage(80, 110, 36, 23, bg); ITU = "BUL"; break;
          case 0xe2: tft.pushImage(80, 110, 36, 23, m1); ITU = "MDR"; break;
          case 0xe3: tft.pushImage(80, 110, 36, 23, nl); ITU = "HOL"; break;
          case 0xe4: tft.pushImage(80, 110, 36, 23, pt); ITU = "POR"; break;
          default: tft.pushImage(80, 110, 36, 23, unknown); ITU = ""; break;
        }
        break;

      case '9':
        switch (radio.ecc) {
          case 0xe0: tft.pushImage(80, 110, 36, 23, al); ITU = "ALB"; break;
          case 0xe1: tft.pushImage(80, 110, 36, 23, dk); ITU = "DNK"; break;
          case 0xe2: tft.pushImage(80, 110, 36, 23, li); ITU = "LIE"; break;
          case 0xe3: tft.pushImage(80, 110, 36, 23, lv); ITU = "LVA"; break;
          case 0xe4: tft.pushImage(80, 110, 36, 23, si); ITU = "SVN"; break;
          default: tft.pushImage(80, 110, 36, 23, unknown); ITU = ""; break;
        }
        break;

      case 'A':
        switch (radio.ecc) {
          case 0xe0: tft.pushImage(80, 110, 36, 23, at); ITU = "AUT"; break;
          case 0xe1: tft.pushImage(80, 110, 36, 23, gi); ITU = "GIB"; break;
          case 0xe2: tft.pushImage(80, 110, 36, 23, is); ITU = "ISL"; break;
          case 0xe3: tft.pushImage(80, 110, 36, 23, lb); ITU = "LBN"; break;
          case 0xe4: tft.pushImage(80, 110, 36, 23, am); ITU = "ARM"; break;
          default: tft.pushImage(80, 110, 36, 23, unknown); ITU = ""; break;
        }
        break;

      case 'B':
        switch (radio.ecc) {
          case 0xe0: tft.pushImage(80, 110, 36, 23, hu); ITU = "HNG"; break;
          case 0xe1: tft.pushImage(80, 110, 36, 23, iq); ITU = "IRQ"; break;
          case 0xe2: tft.pushImage(80, 110, 36, 23, mc); ITU = "MCO"; break;
          case 0xe3: tft.pushImage(80, 110, 36, 23, az); ITU = "AZE"; break;
          case 0xe4: tft.pushImage(80, 110, 36, 23, uz); ITU = "UZB"; break;
          default: tft.pushImage(80, 110, 36, 23, unknown); ITU = ""; break;
        }
        break;

      case 'C':
        switch (radio.ecc) {
          case 0xe0: tft.pushImage(80, 110, 36, 23, mt); ITU = "MLT"; break;
          case 0xe1: tft.pushImage(80, 110, 36, 23, gb); ITU = "G"; break;
          case 0xe2: tft.pushImage(80, 110, 36, 23, lt); ITU = "LTU"; break;
          case 0xe3: tft.pushImage(80, 110, 36, 23, hr); ITU = "HRV"; break;
          case 0xe4: tft.pushImage(80, 110, 36, 23, ge); ITU = "GEO"; break;
          default: tft.pushImage(80, 110, 36, 23, unknown); ITU = ""; break;
        }
        break;

      case 'D':
        switch (radio.ecc) {
          case 0xe0: tft.pushImage(80, 110, 36, 23, de); ITU = "D"; break;
          case 0xe1: tft.pushImage(80, 110, 36, 23, ly); ITU = "LBY"; break;
          case 0xe2: tft.pushImage(80, 110, 36, 23, rs); ITU = "SRB"; break;
          case 0xe3: tft.pushImage(80, 110, 36, 23, kz); ITU = "KAZ"; break;
          default: tft.pushImage(80, 110, 36, 23, unknown); ITU = ""; break;
        }
        break;

      case 'E':
        switch (radio.ecc) {
          case 0xe0: tft.pushImage(80, 110, 36, 23, c1); ITU = "CNR"; break;
          case 0xe1: tft.pushImage(80, 110, 36, 23, ro); ITU = "ROU"; break;
          case 0xe2: tft.pushImage(80, 110, 36, 23, es); ITU = "E"; break;
          case 0xe3: tft.pushImage(80, 110, 36, 23, se); ITU = "S"; break;
          case 0xe4: tft.pushImage(80, 110, 36, 23, tm); ITU = "TKM"; break;
          default: tft.pushImage(80, 110, 36, 23, unknown); ITU = ""; break;
        }
        break;

      case 'F':
        switch (radio.ecc) {
          case 0xe0: tft.pushImage(80, 110, 36, 23, eg); ITU = "EGY"; break;
          case 0xe1: tft.pushImage(80, 110, 36, 23, fr); ITU = "F"; break;
          case 0xe2: tft.pushImage(80, 110, 36, 23, no); ITU = "NOR"; break;
          case 0xe3: tft.pushImage(80, 110, 36, 23, by); ITU = "BLR"; break;
          case 0xe4: tft.pushImage(80, 110, 36, 23, ba); ITU = "BIH"; break;
          default: tft.pushImage(80, 110, 36, 23, unknown); ITU = ""; break;
        }
        break;
      default: tft.pushImage(80, 110, 36, 23, unknown); ITU = ""; break;
    }
    tftReplace(0, ITUold, ITU, 97, 140, SecondaryColor, SecondaryColorSmooth, BackgroundColor3, 16);
    eccold = radio.ecc;
    ITUold = ITU;
  }
}

void ShowMemoryPos(void) {
  if (!IsStationEmpty()) {
    EEPROM.writeByte(EE_BYTE_MEMORYPOS, memorypos);
    EEPROM.commit();
  }
  int memposcolor = 0;
  int memposcolorsmooth = 0;
  switch (memoryposstatus) {
    case MEM_DARK:
      memposcolor = InsignificantColor;
      memposcolorsmooth = InsignificantColorSmooth;
      break;

    case MEM_NORMAL:
      memposcolor = PrimaryColor;
      memposcolorsmooth = PrimaryColorSmooth;
      break;

    case MEM_EXIST:
      memposcolor = SignificantColor;
      memposcolorsmooth = SignificantColorSmooth;
      break;
  }
  tftReplace(-1, String(memoryposold + 1), String(memorypos + 1), 93, 65, memposcolor, memposcolorsmooth, BackgroundColor2, 16);
  memoryposold = memorypos;
}

void ShowVolume(void) {
  uint8_t segments = map(volume, 0, 63, 0, 100);
  tft.pushImage(25, 46, 270, 50, volumebackground);
  OneBigLineSprite.pushImage(0, 0, 270, 50, volumebackground);
  if (segments > 100) segments = 100;
  OneBigLineSprite.fillRect(60, 9, 2 * segments, 9, BarInsignificantColor);
  OneBigLineSprite.pushSprite(25, 46);
  tftPrint(0, String(map(volume, 0, 62, 0, 100)), 190, 68, ActiveColor, ActiveColorSmooth, 28);
  Headphones.SetVolume(volume);
  EEPROM.writeByte(EE_BYTE_VOLUME, volume);
  EEPROM.commit();
  VolumeTimer = millis();
}


// Signal-level meter (RSSI bar). 100 ms throttle so quick fluctuations don't
// flood the SPI bus; the rest is just the standard diff-vs-old logic.
void ShowSignalLevel(void) {
  if (millis() - rssiTimer >= 100) {
    rssiTimer = millis();
    CNR = radio.cnr;
  }

  SAvg = (((SAvg * 9) + 5) / 10) + SignalLevel;
  SAvg2 = (((SAvg2 * 9) + 5) / 10) + CNR;

  SignalLevel = SAvg / 10;
  CNR = SAvg2 / 10;

  int SignalLevelprint = 0;
  if (unit == 0) SignalLevelprint = SignalLevel;
  if (unit == 1) SignalLevelprint = ((SignalLevel * 100) + 10875) / 100;
  if (unit == 2) SignalLevelprint = round((float(SignalLevel) / 10.0 - 10.0 * log10(75) - 90.0) * 10.0);

  if (!ShowServiceInformation) {
    if (SignalLevelprint > (SignalLevelold + 3) || SignalLevelprint < (SignalLevelold - 3) || displayreset) {
      ShortSprite.fillSprite(BackgroundColor3);
      ShortSprite.setTextDatum(TR_DATUM);
      ShortSprite.setTextColor(PrimaryColor, PrimaryColorSmooth, false);
      ShortSprite.drawString(String(SignalLevelprint / 10) + "." + String(abs(SignalLevelprint % 10)), 35, 0);
      ShortSprite.pushSprite(146, 109);

      byte segments = 0;
      if (SignalLevel > 120) {
        segments = map(SignalLevel, 100, 700, 0, 85);
      }

      byte constrainedSegments = segments;
      byte significantSegments = segments;

      if (constrainedSegments > 85) constrainedSegments = 85;
      if (significantSegments > 85) significantSegments = 85;

      int length1 = 2 * segments;
      int length2 = 2 * (significantSegments - 56);
      int length3 = 2 * (85 - constrainedSegments);

      tft.fillRect(134, 129, length1, 6, BarInsignificantColor);
      tft.fillRect(134 + 2 * 56, 129, length2, 6, BarSignificantColor);
      tft.fillRect(134 + 2 * constrainedSegments, 129, length3, 6, GreyoutColor);

      SignalLevelold = SignalLevelprint;
    }

    if (CNRold != CNR || displayreset) {
      if (radio.signallock) {
        tftPrint(1, String("--"), 289, 109, BackgroundColor, BackgroundColor3, 16);
        tftReplace(1, String(CNRold), String(CNR), 289, 109, PrimaryColor, PrimaryColorSmooth, BackgroundColor3, 16);
      } else {
        tftReplace(1, String(CNRold), "--", 289, 109, PrimaryColor, PrimaryColorSmooth, BackgroundColor3, 16);
      }
      CNRold = CNR;
    }

    if (ficold != radio.fic || displayreset) {
      byte quality = map(radio.fic, 0, 100, 139, 0);
      for (byte x = 0; x < 10; x++) tft.pushImage (135, 91 + x, 139, 1, QualLine);
      tft.fillRect(274 - quality, 91, quality, 10, BackgroundColor3);
      tftReplace(1, String(ficold) + "%", String(radio.fic) + "%", 315, 90, PrimaryColor, PrimaryColorSmooth, BackgroundColor3, 16);
      ficold = radio.fic;
    }


  } else {
    String SignalLevelString = String(String(SignalLevelprint / 10)) + "." + String(abs(SignalLevelprint % 10));
    if ((SignalLevelString != SignalLeveloldString && !setvolume) || displayreset) {
      tftReplace(1, SignalLeveloldString, SignalLevelString, 191, 56, PrimaryColor, PrimaryColorSmooth, BackgroundColor3, 16);
      SignalLeveloldString = SignalLevelString;
    }

    if (((CNRold != CNR) && !setvolume) || displayreset) {
      tftReplace(1, String(CNRold), String(CNR), 284, 56, PrimaryColor, PrimaryColorSmooth, BackgroundColor3, 16);
      CNRold = CNR;
    }
  }
}

void ShowBitrate(void) {
  if (tuning) radio.bitrate = 0;
  if (radio.bitrate != BitrateOld || displayreset) {
    MediumSprite.pushImage(-9, -140, 320, 240, Background);
    MediumSprite.setTextDatum(TC_DATUM);
    MediumSprite.setTextColor(PrimaryColor, PrimaryColorSmooth, false);
    MediumSprite.drawString((radio.bitrate != 0 && radio.ServiceStart && !tuning ? String (radio.bitrate, DEC) + " kbit/s" : ""), 30, 0);
    MediumSprite.pushSprite(9, 140);
    BitrateOld = radio.bitrate;
  }
}

void ShowClock(void) {
  if (radio.signallock) setTime(radio.Hours, radio.Minutes, radio.Seconds, radio.Days, radio.Months, radio.Year);
  String clockstring = (hour() < 10 ? "0" : "") + String(hour()) + ":" + (minute() < 10 ? "0" : "") + String(minute());
  String datestring = (day() < 10 ? "0" : "") + String(day()) + "-" + (month() < 10 ? "0" : "") + String(month()) + "-" + String(year());
  if (clockstringOld != clockstring || displayreset) {
    ShortSprite.pushImage(-105, -7, 320, 240, Background);
    ShortSprite.setTextDatum(TL_DATUM);
    ShortSprite.setTextColor(ActiveColor, ActiveColorSmooth, false);
    ShortSprite.drawString(clockstring, 0, 0);
    ShortSprite.pushSprite(105, 7);
    clockstringOld = clockstring;
  }

  if (datestringOld != datestring || displayreset) {
    MediumSprite.pushImage(-177, -7, 320, 240, Background);
    MediumSprite.setTextDatum(TL_DATUM);
    MediumSprite.setTextColor(ActiveColor, ActiveColorSmooth, false);
    MediumSprite.drawString(datestring, 0, 0);
    MediumSprite.pushSprite(177, 7);
    datestringOld = datestring;
  }
}

void ShowSlideShowIcon(void) {
  if (SlideShowAvailableOld != radio.SlideShowAvailable || displayreset) {
    if (radio.SlideShowAvailable) {
      tft.pushImage (10, 187, 30, 22, slideshowon);
    } else {
      tft.pushImage (10, 187, 30, 22, slideshowoff);
    }
    SlideShowAvailableOld = radio.SlideShowAvailable;
  }
}

void ShowTuneMode(void) {
  ModeSprite.pushImage(-6, -33, 320, 240, Background);

  switch (tunemode) {
    case TUNE_MAN:
      ModeSprite.setTextColor(ActiveColor, ActiveColorSmooth, false);
      ModeSprite.drawString("MAN", 23, 0);
      ModeSprite.setTextColor(SecondaryColor, SecondaryColorSmooth, false);
      ModeSprite.drawString("AUTO", 23, 16);
      ModeSprite.drawString("MEM", 23, 32);
      break;

    case TUNE_AUTO:
      ModeSprite.setTextColor(ActiveColor, ActiveColorSmooth, false);
      ModeSprite.drawString("AUTO", 23, 16);
      ModeSprite.setTextColor(SecondaryColor, SecondaryColorSmooth, false);
      ModeSprite.drawString("MAN", 23, 0);
      ModeSprite.drawString("MEM", 23, 32);
      break;

    case TUNE_MEM:
      ModeSprite.setTextColor(SecondaryColor, SecondaryColorSmooth, false);
      ModeSprite.drawString("MAN", 23, 0);
      ModeSprite.drawString("AUTO", 23, 16);

      if (memorystore) {
        ModeSprite.setTextColor(SignificantColor, SignificantColorSmooth, false);
      } else {
        ModeSprite.setTextColor(ActiveColor, ActiveColorSmooth, false);
      }
      ModeSprite.drawString("MEM", 23, 32);
      break;
  }
  ModeSprite.pushSprite(6, 33);
  EEPROM.writeByte(EE_BYTE_TUNEMODE, tunemode);
  EEPROM.commit();
}
